Laurenx618/ENGR3430-Eclectronics-FinalProject/Final_project/3D/TL3301AFxxxxJ.stp

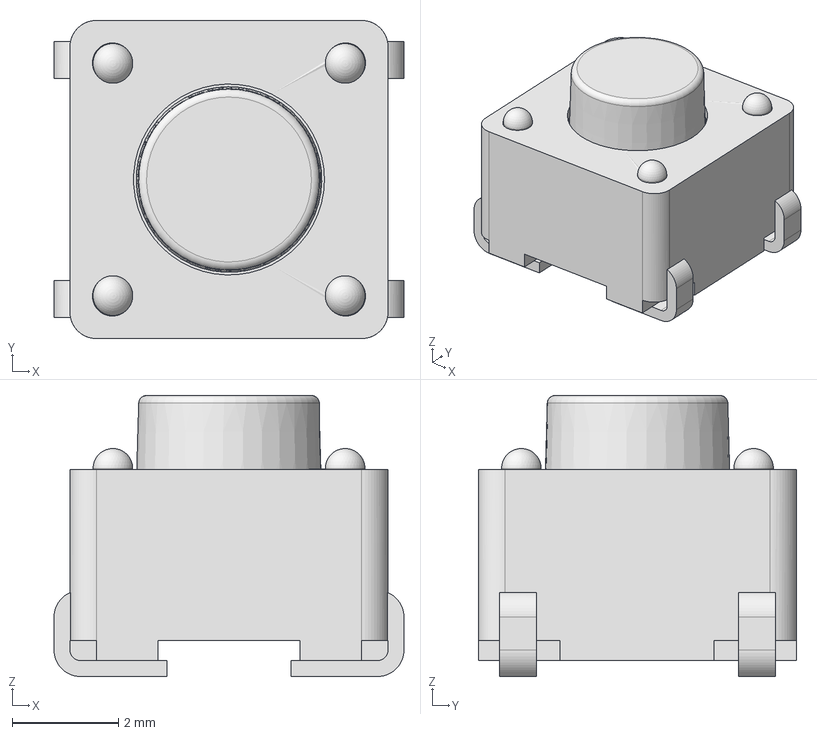
[picture p15: CAD file, 2022-11-29]
Final_project/3D/TL3301AFxxxxJ.stp
6.60 x 6.00 x 5.30 mm
