Laurenx618/ENGR3430-Eclectronics-FinalProject/Final_project/3D/UFQFPN48.stp

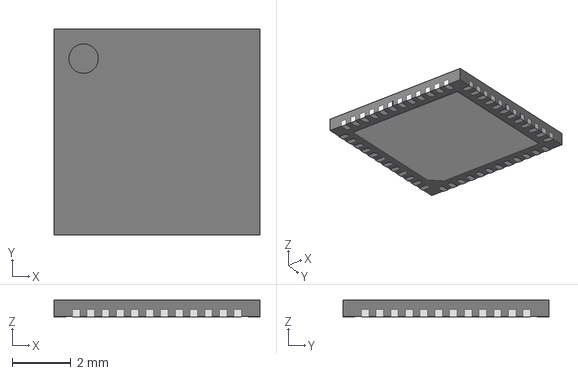
[picture p16: CAD file, 2022-11-29]
Final_project/3D/UFQFPN48.stp
7.00 x 7.00 x 0.57 mm
