Laurenx618/ENGR3430-Eclectronics-FinalProject/Final_project/3D/CUI_SDS-50J.step

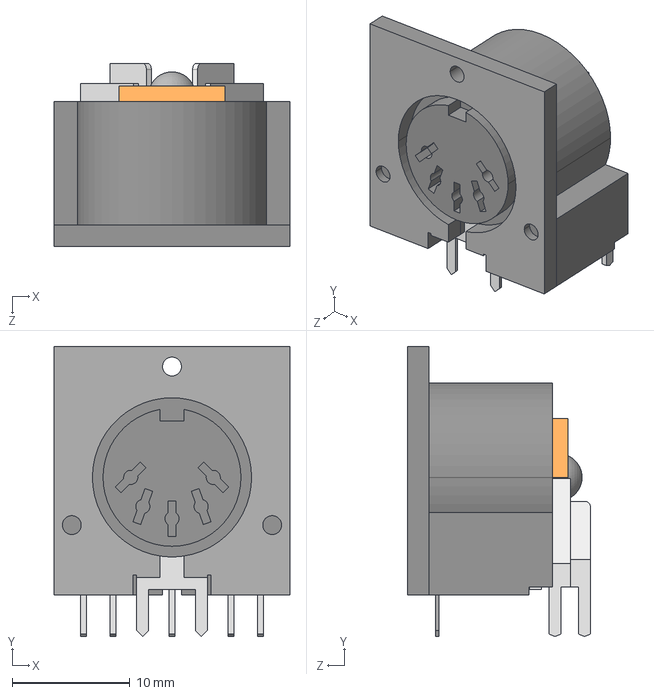
[picture p17: CAD file, 2022-11-29]
Final_project/3D/CUI_SDS-50J.step
20.0 x 24.6 x 15.5 mm
