Laurenx618/ENGR3430-Eclectronics-FinalProject/Final_project/3D/ABM10.STP

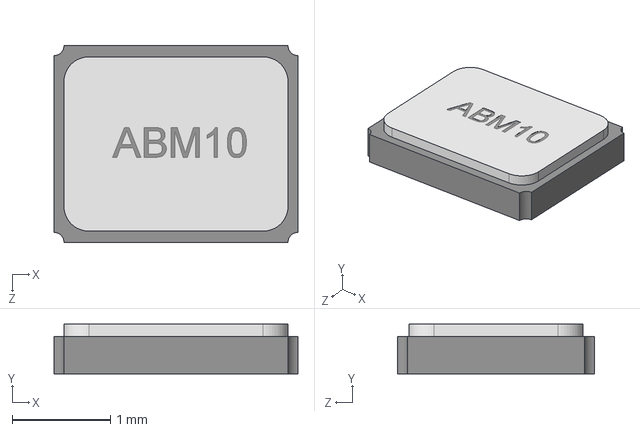
[picture p18: CAD file, 2022-11-29]
Final_project/3D/ABM10.STP
2.49 x 0.508 x 2.01 mm
