Laurenx618/ENGR3430-Eclectronics-FinalProject/Final_project/3D/CSTNE.step

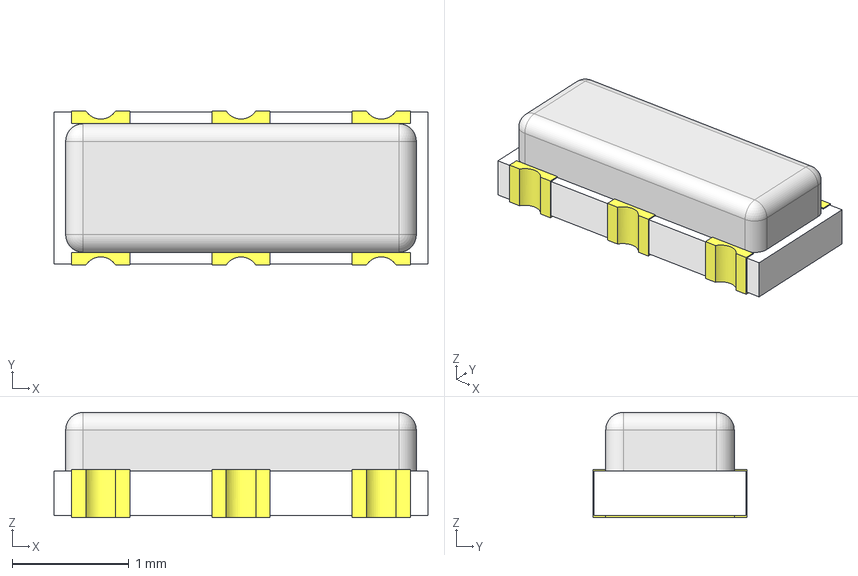
[picture p19: CAD file, 2022-11-29]
Final_project/3D/CSTNE.step
3.20 x 1.32 x 0.9 mm
