Laurenx618/ENGR3430-Eclectronics-FinalProject/Final_project/3D/3382g-001-xxx.stp

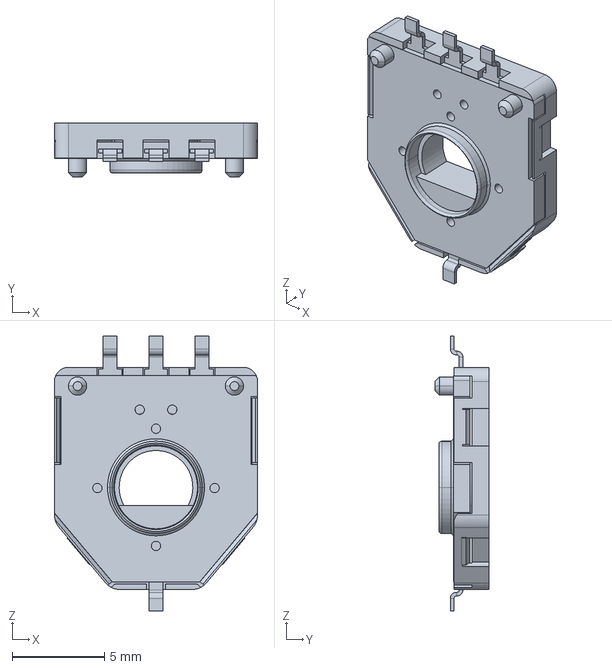
[picture p20: CAD file, 2022-11-29]
Final_project/3D/3382g-001-xxx.stp
11.0 x 2.95 x 14.9 mm
