Laurenx618/ENGR3430-Eclectronics-FinalProject/Final_project/3D/WS2812-2020.STEP

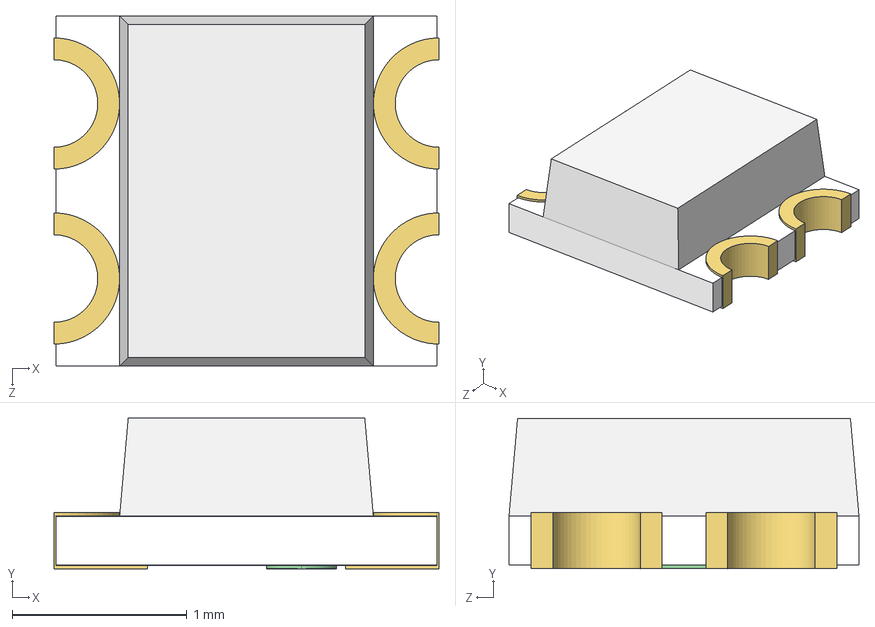
[picture p21: CAD file, 2022-11-29]
Final_project/3D/WS2812-2020.STEP
2.20 x 0.86 x 2.00 mm
