Laurenx618/ENGR3430-Eclectronics-FinalProject/Final_project/3D/QFN-32_5x5.stp

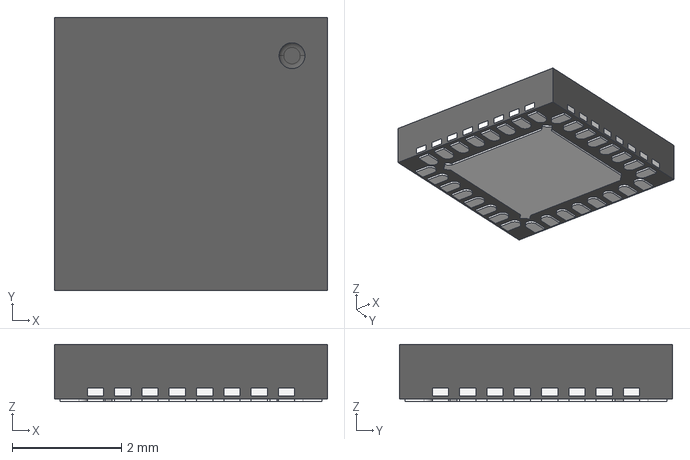
[picture p22: CAD file, 2022-11-29]
Final_project/3D/QFN-32_5x5.stp
5.00 x 5.00 x 1.05 mm
