Laurenx618/ENGR3430-Eclectronics-FinalProject/Micropython_code/ili9341_test/mySetup.py

from ili9341 import Display
from machine import Pin, SPI

TFT_CLK_PIN = const(10)
TFT_MOSI_PIN = const(11)
#TFT_MISO_PIN = const(4)

TFT_CS_PIN = const(13)
TFT_RST_PIN = const(14)
TFT_DC_PIN = const(15)

def createMyDisplay():
    #spi = SPI(0, baudrate=40000000, sck=Pin(TFT_CLK_PIN), mosi=Pin(TFT_MOSI_PIN))
    spiTFT = SPI(0, baudrate=51200000,
                 sck=Pin(TFT_CLK_PIN), mosi=Pin(TFT_MOSI_PIN))
    display = Display(spiTFT,
                      dc=Pin(TFT_DC_PIN), cs=Pin(TFT_CS_PIN), rst=Pin(TFT_RST_PIN))
    return display
